inkfish/lander-control/hardware/misc/signal-2023-07-29-151037_002.png

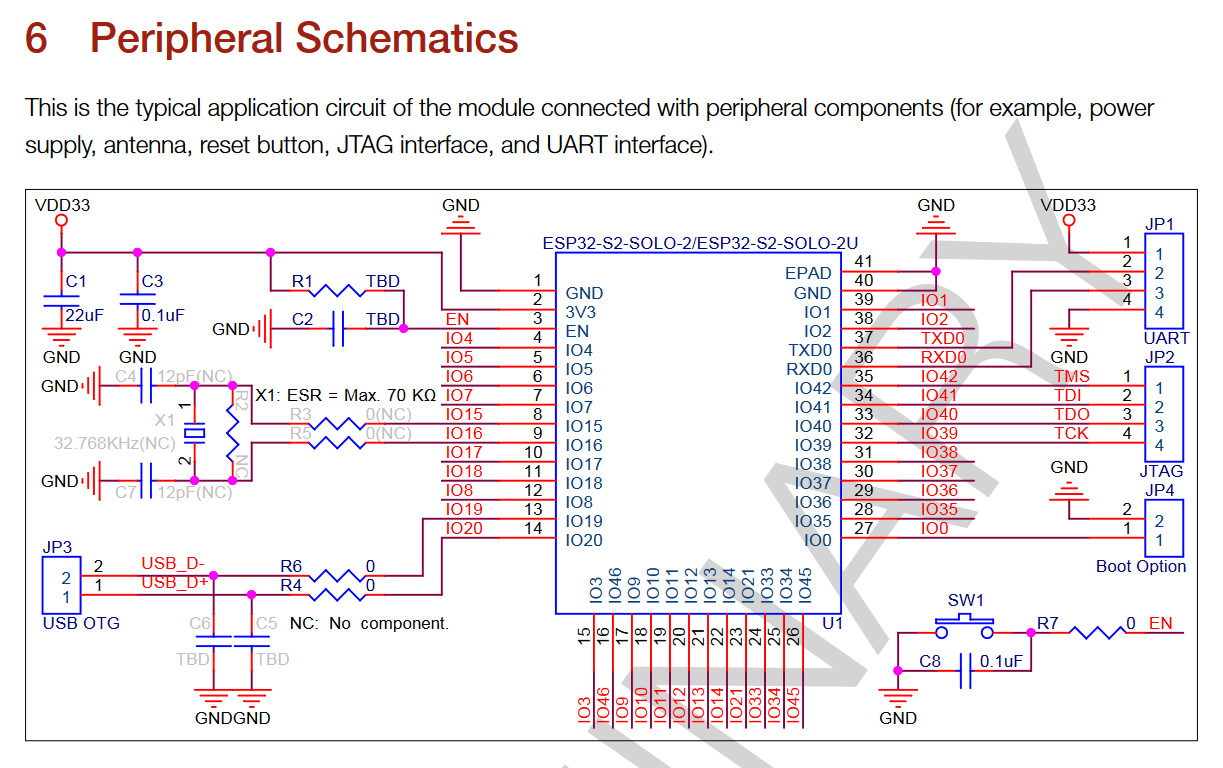
hardware/misc/signal-2023-07-29-151037_002.png
