inkfish/lander-control/hardware/misc/signal-2023-07-29-175642_002.png

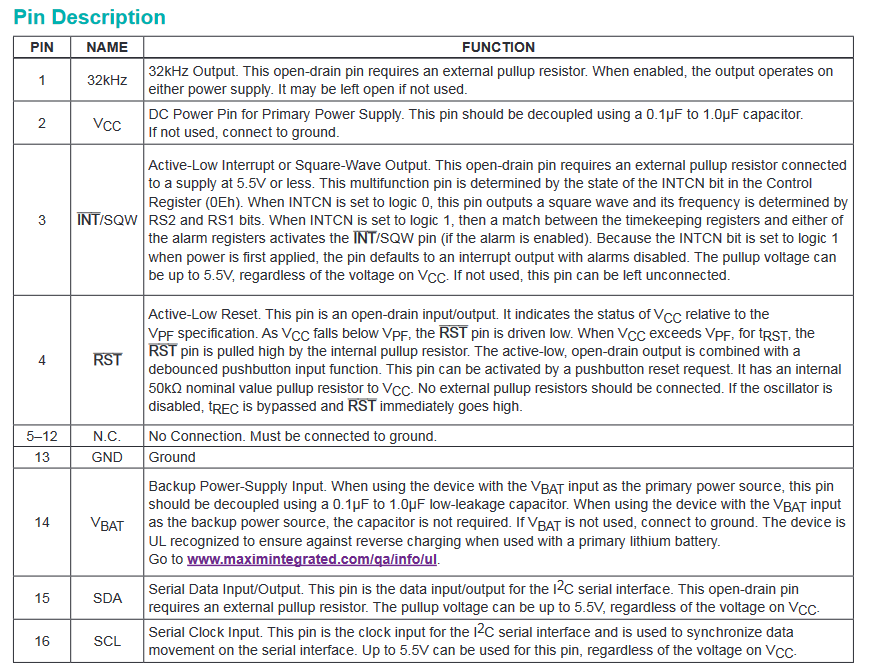
hardware/misc/signal-2023-07-29-175642_002.png
