inkfish/lander-control/hardware/misc/signal-2023-07-29-180950_002.png

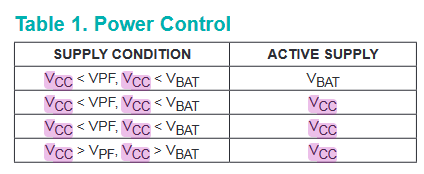
hardware/misc/signal-2023-07-29-180950_002.png
